apoorvanova/EcoNode/schematic/EduNode_schematic.kicad_sch

## KiCad design schematic/EduNode_schematic.kicad_sch (2026-09-04)

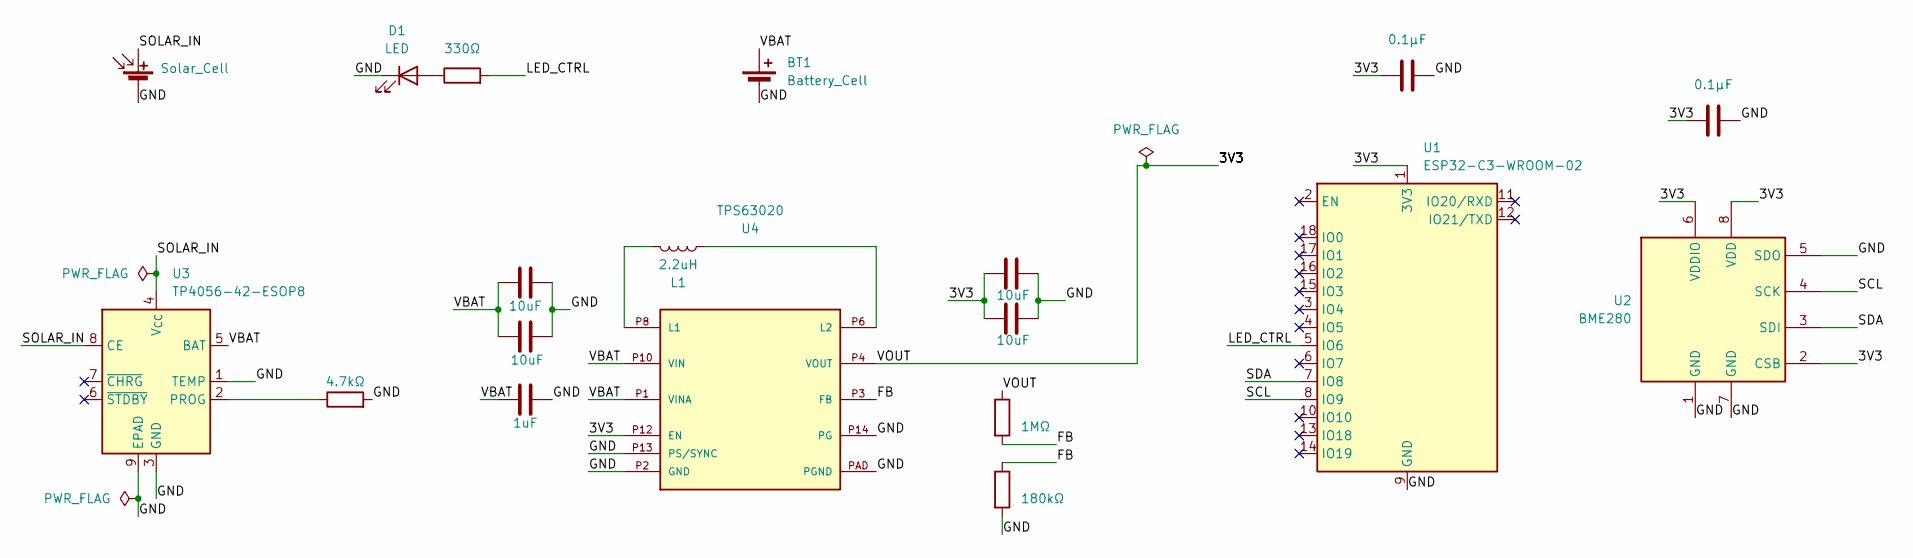
[picture p4: schematic EduNode_schematic.kicad_sch]

Parts:
BT1: Battery_Cell
C1, C2, C5, C6: 10uF
C3: 1uF
C7, C8: 0.1µF
D1: LED
L1: 2.2uH
R1: 1MΩ
R2: 180kΩ
R3: 330Ω
R4: 4.7kΩ
SC1: Solar_Cell
U1: ESP32-C3-WROOM-02
U2: BME280; Bosch_LGA-8_2.5x2.5mm_P0.65mm_ClockwisePinNumbering
U3: TP4056-42-ESOP8; SOIC-8-1EP_3.9x4.9mm_P1.27mm_EP2.41x3.3mm_ThermalVias
U4: TPS63020; QFN14_1

Connections:
3V3: C5.1, C6.1, C7.1, C8.1, R1.1, U1.1 (3V3), U2.2 (CSB), U2.6 (VDDIO), U2.8 (VDD), U4.P4 (VOUT), U4.P5 (VOUT), U4.P12 (EN)
FB: R1.2, R2.1, U4.P3 (FB)
GND: BT1.2 (-), C1.2, C2.2, C3.2, C5.2, C6.2, C7.2, C8.2, D1.1 (K), R2.2, R4.2, SC1.2 (-), U1.9 (GND), U1.19 (GND), U2.1 (GND), U2.5 (SDO), U2.7 (GND), U3.1 (TEMP), U3.3 (GND), U3.9 (EPAD), U4.P2 (GND), U4.P13 (PS/SYNC), U4.P14 (PG), U4.PAD (PGND)
LED_CTRL: R3.2, U1.5 (IO6)
unnamed: D1.2 (A), R3.1
unnamed: L1.1, U4.P6 (L2), U4.P7 (L2)
unnamed: L1.2, U4.P8 (L1), U4.P9 (L1)
unnamed: R4.1, U3.2 (PROG)
SCL: U1.8 (IO9), U2.4 (SCK)
SDA: U1.7 (IO8), U2.3 (SDI)
SOLAR_IN: SC1.1 (+), U3.4 (V_{CC}), U3.8 (CE)
VBAT: BT1.1 (+), C1.1, C2.1, C3.1, U3.5 (BAT), U4.P1 (VINA), U4.P10 (VIN), U4.P11 (VIN)
